joenuK/woodfired-pizzaoven-german/doc/draufsicht.jpeg

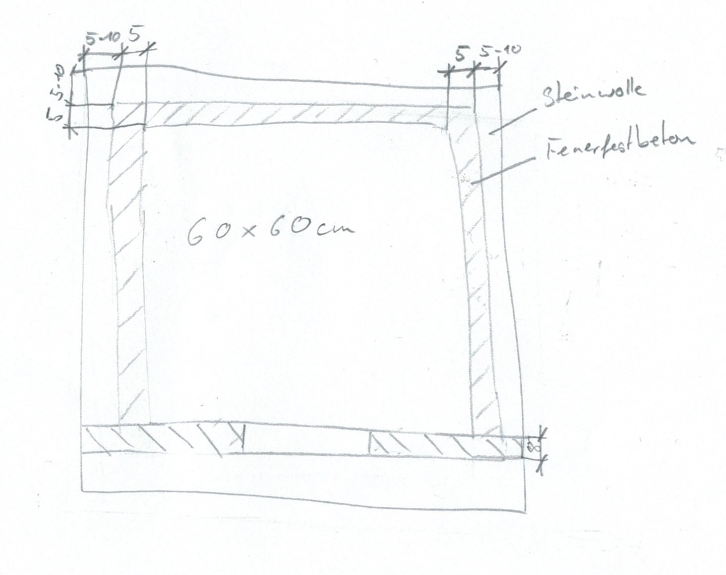
doc/draufsicht.jpeg
