joenuK/woodfired-pizzaoven-german/doc/frontansicht.jpeg

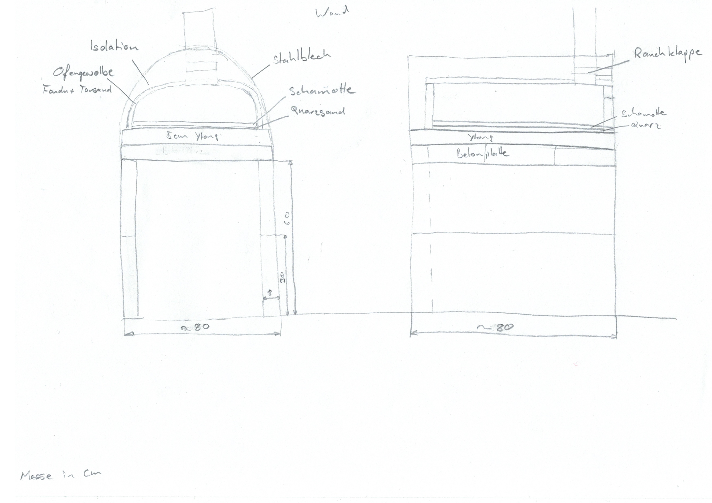
doc/frontansicht.jpeg
