joenuK/woodfired-pizzaoven-german/img/einzelteile/IMG_4779.JPG

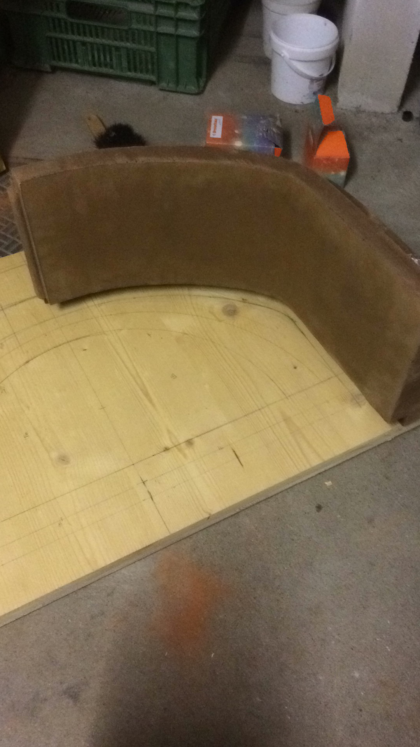
img/einzelteile/IMG_4779.JPG
