joenuK/woodfired-pizzaoven-german/img/einzelteile/IMG_4780.JPG

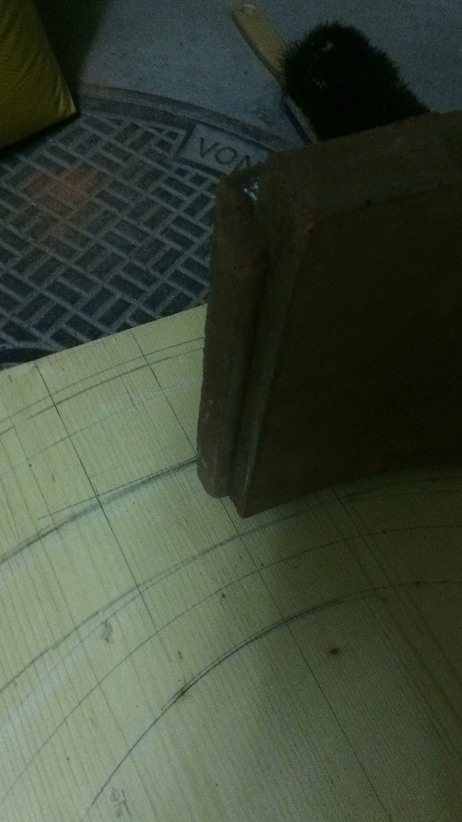
img/einzelteile/IMG_4780.JPG
