joenuK/woodfired-pizzaoven-german/img/einzelteile/IMG_4781.JPG

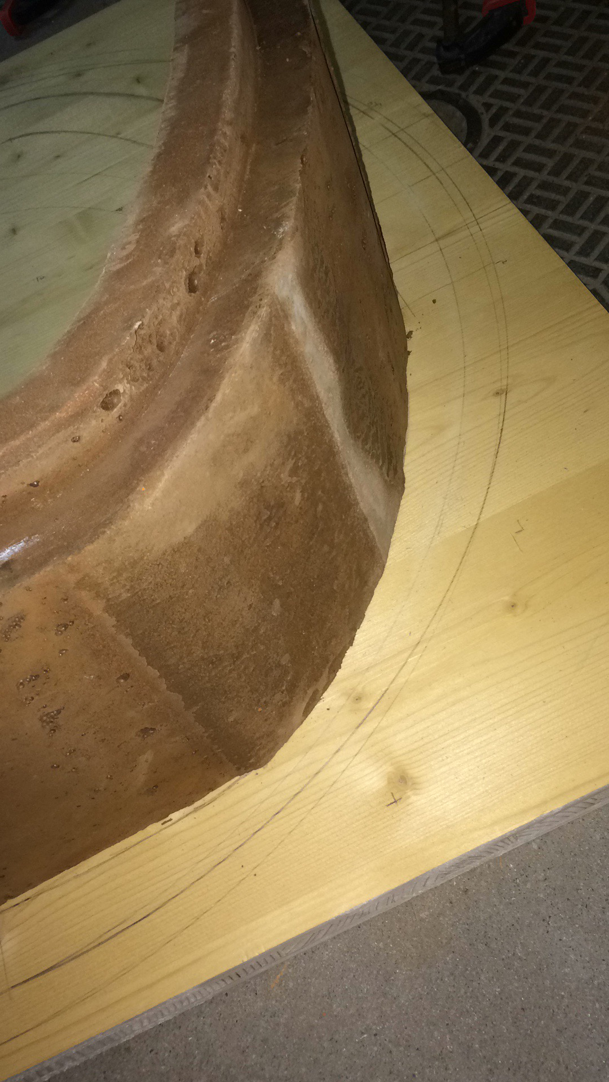
img/einzelteile/IMG_4781.JPG
