joenuK/woodfired-pizzaoven-german/img/endprodukt/IMG_5551.JPG

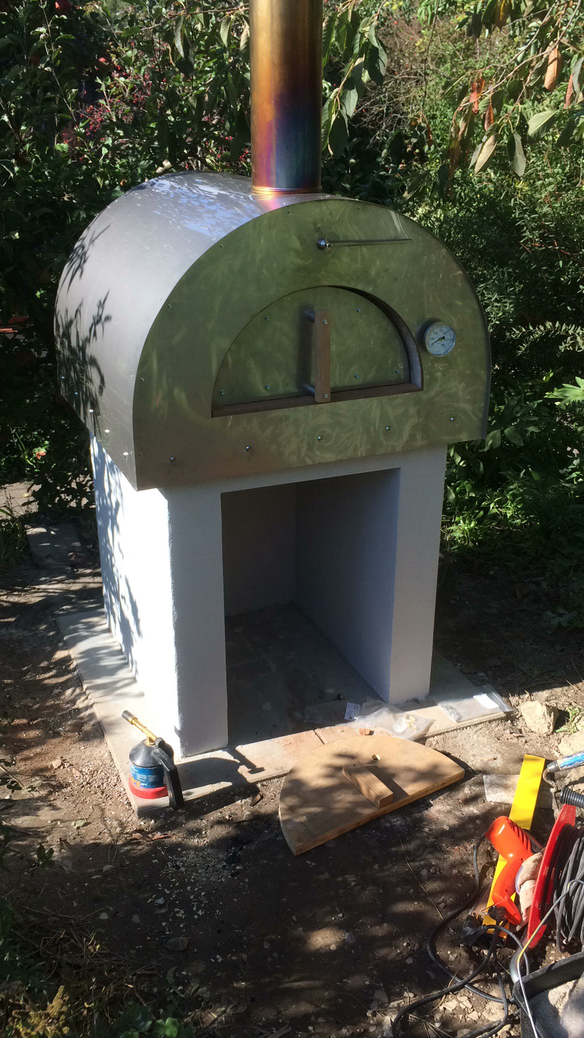
img/endprodukt/IMG_5551.JPG
