joenuK/woodfired-pizzaoven-german/img/endprodukt/IMG_5552.JPG

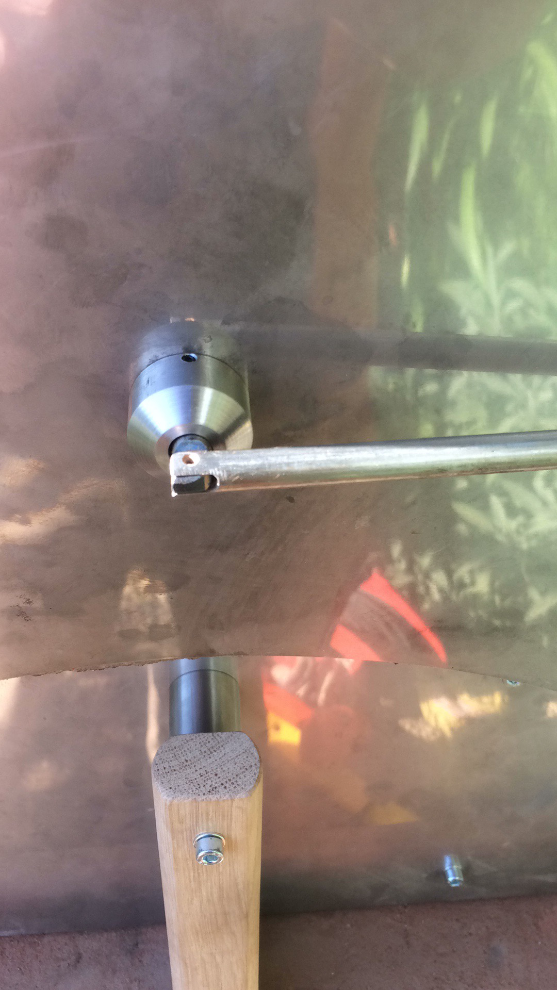
img/endprodukt/IMG_5552.JPG
