joenuK/woodfired-pizzaoven-german/img/endprodukt/IMG_5553.JPG

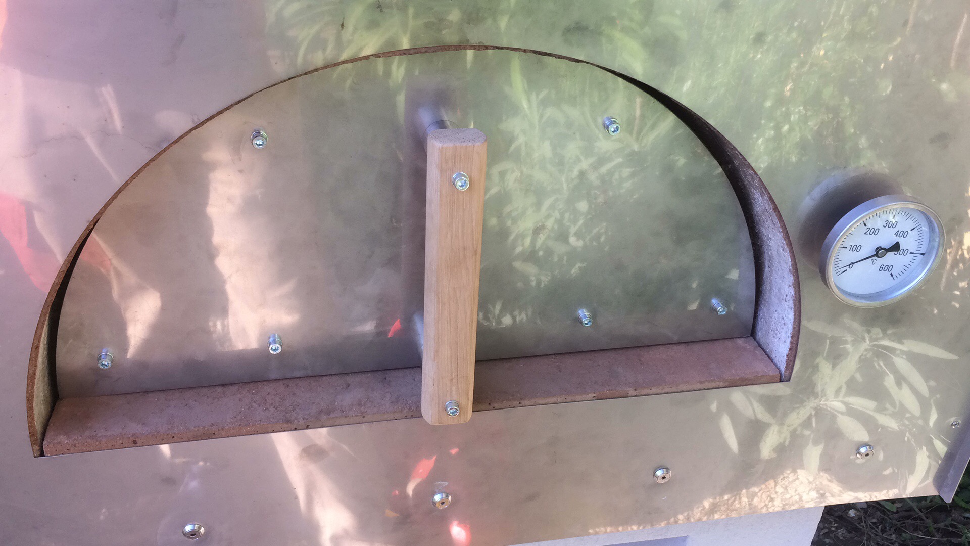
img/endprodukt/IMG_5553.JPG
