joenuK/woodfired-pizzaoven-german/img/endprodukt/thumb_4df1.jpg

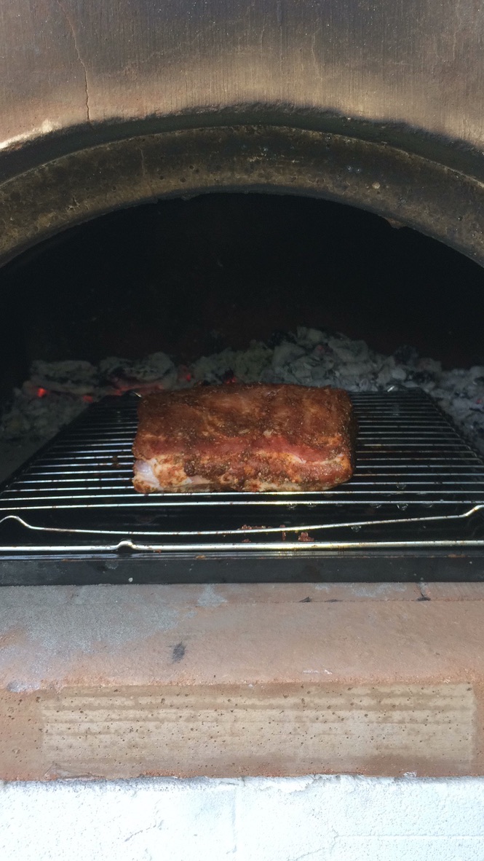
img/endprodukt/thumb_4df1.jpg
