joenuK/woodfired-pizzaoven-german/img/schalung/IMG_4768.JPG

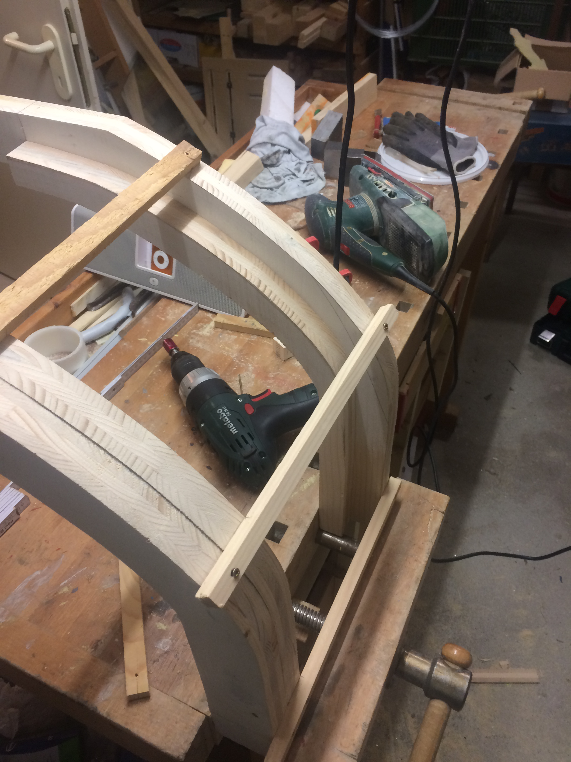
img/schalung/IMG_4768.JPG
