joenuK/woodfired-pizzaoven-german/img/schalung/IMG_4769.JPG

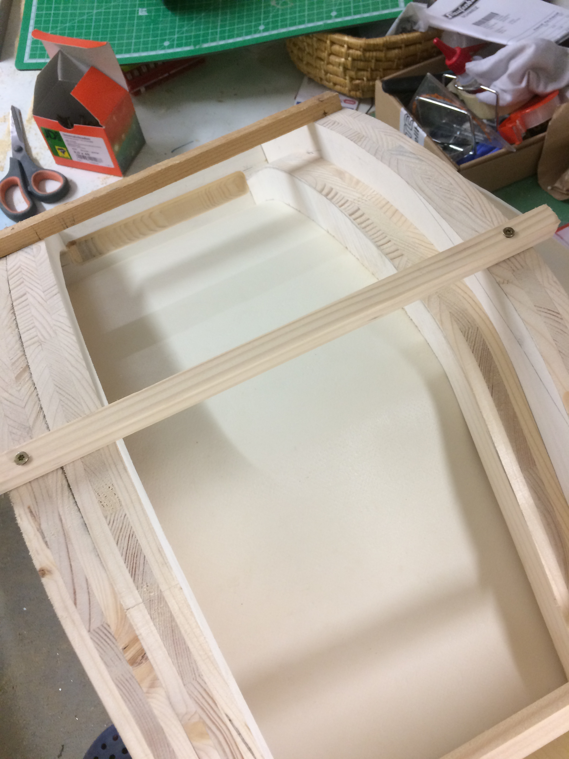
img/schalung/IMG_4769.JPG
