joenuK/woodfired-pizzaoven-german/img/schalung/IMG_5558.JPG

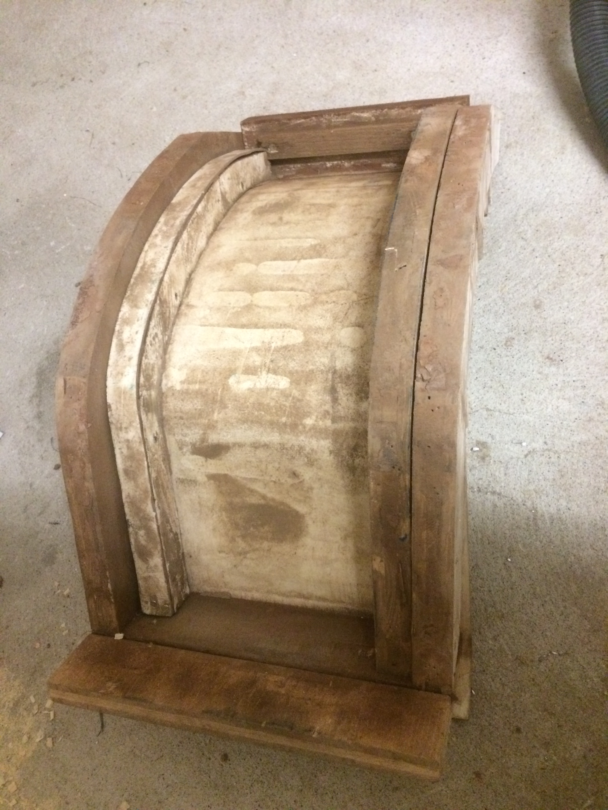
img/schalung/IMG_5558.JPG
