joenuK/woodfired-pizzaoven-german/img/schalung/IMG_5559.JPG

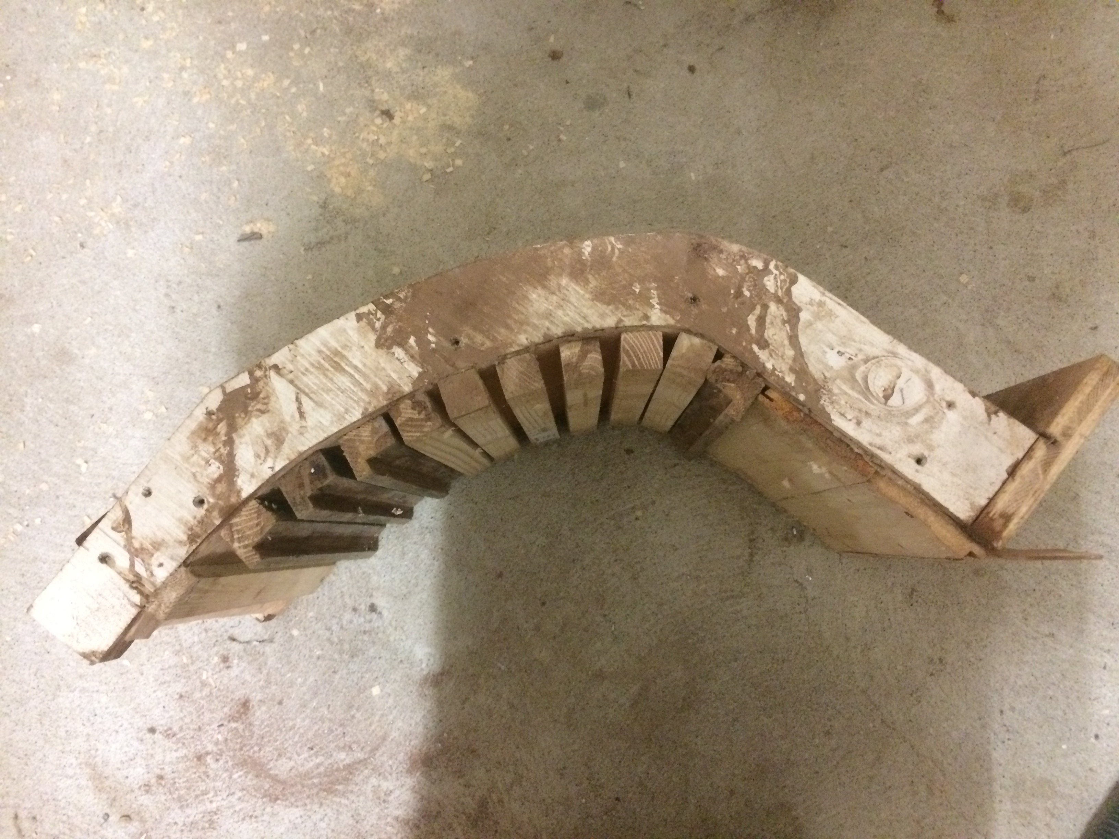
img/schalung/IMG_5559.JPG
