joenuK/woodfired-pizzaoven-german/img/schalung/IMG_5560.JPG

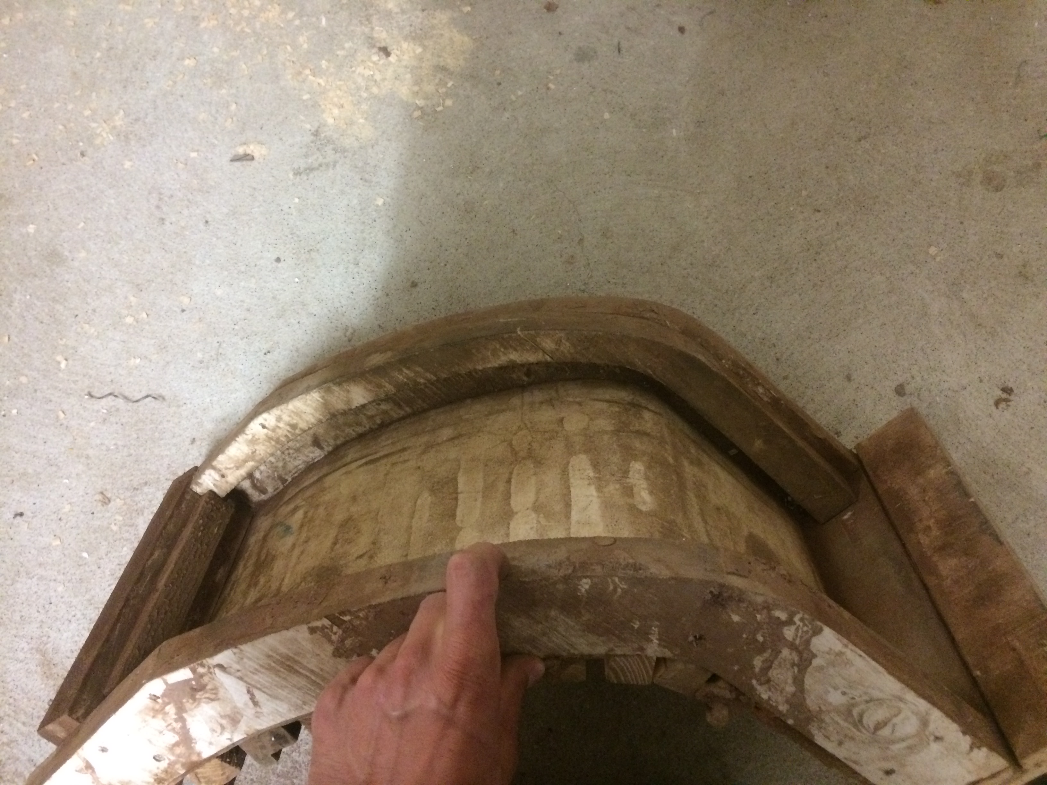
img/schalung/IMG_5560.JPG
