joenuK/woodfired-pizzaoven-german/img/aufbau/IMG_4809.JPG

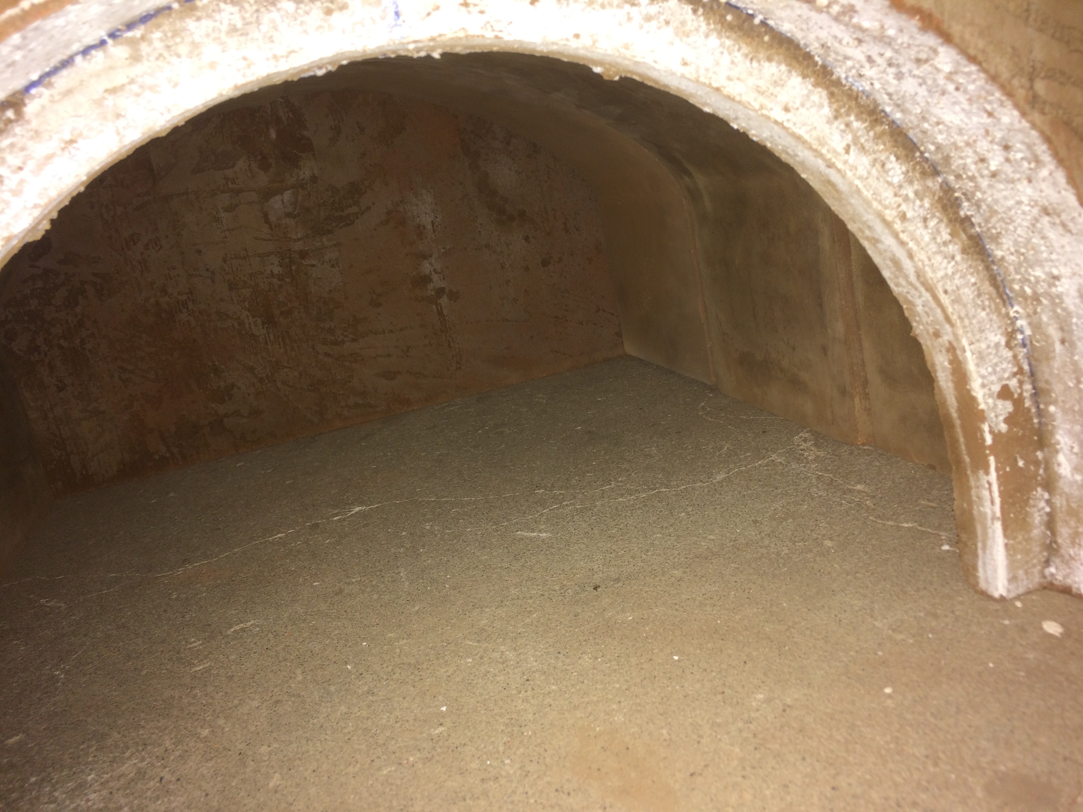
img/aufbau/IMG_4809.JPG
