joenuK/woodfired-pizzaoven-german/img/aufbau/IMG_4841.JPG

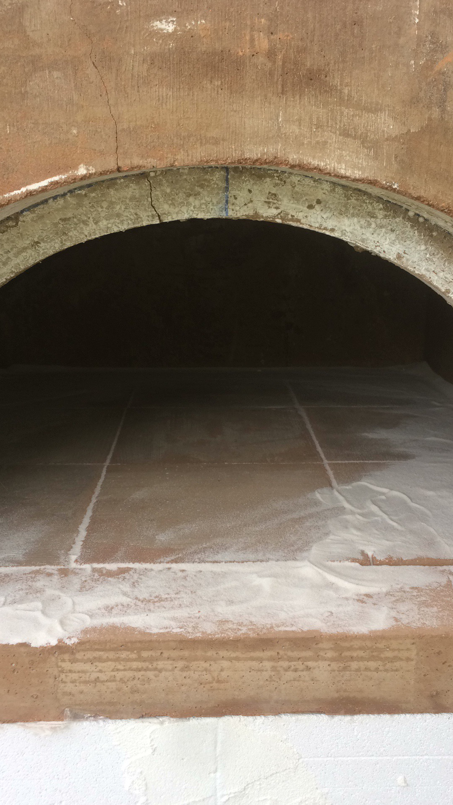
img/aufbau/IMG_4841.JPG
