joenuK/woodfired-pizzaoven-german/img/aufbau/IMG_5534.JPG

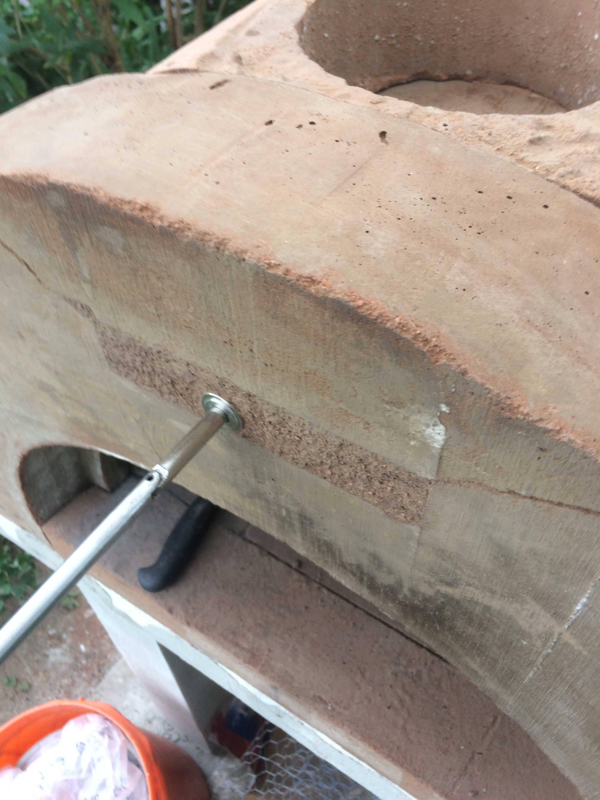
img/aufbau/IMG_5534.JPG
