joenuK/woodfired-pizzaoven-german/img/aufbau/IMG_5550.JPG

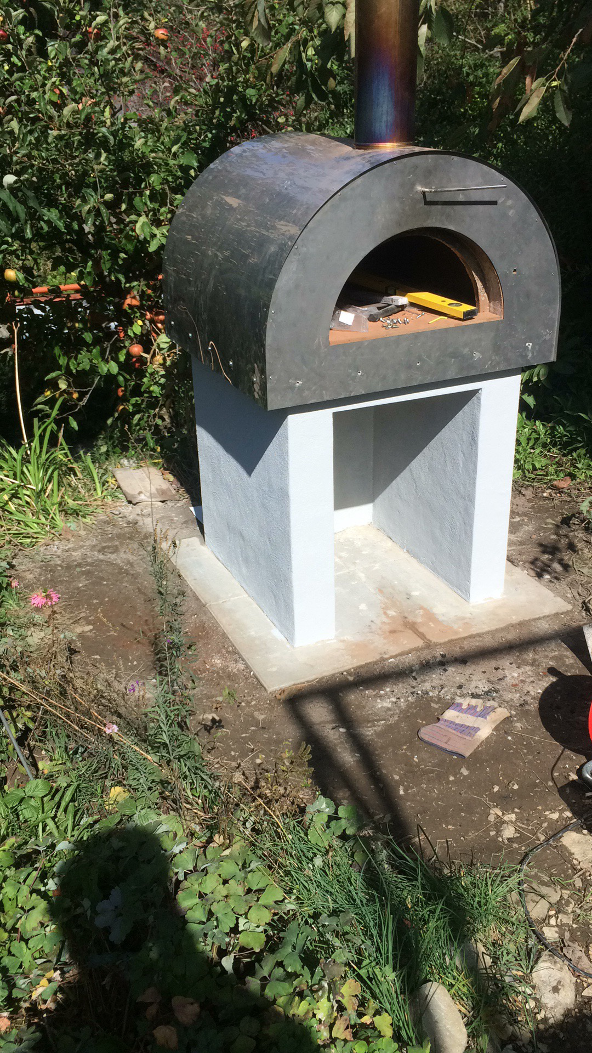
img/aufbau/IMG_5550.JPG
